MaxLiebe/Hydration-Tracker/src/arduino/hydration-tracker/logo.h

//To change the logo, convert an image to a resolution below 128x64. For the best results, also try to convert it to duo color (black & white).
//Now, use an online converter like https://www.online-utility.org/image/convert/to/XBM or https://convertio.co/png-xbm/ to convert your image to an XBM image.
//Open your downloaded XBM image in notepad and copy the array bytes to the LOGO_BITS array down below. Also make sure the resolution in LOGO_WIDTH and LOGO_HEIGHT is correct.

#define LOGO_WIDTH 120
#define LOGO_HEIGHT 58
static uint8_t LOGO_BITS[] = { 
0x00, 0x00, 0x00, 0x00, 0x00, 0x00, 0x00, 0x00, 0x00, 0x00, 0x00, 0x00, 
  0x00, 0x00, 0x00, 0x00, 0x00, 0x00, 0x00, 0x00, 0x00, 0x00, 0x00, 0x00, 
  0x00, 0x00, 0x00, 0x00, 0x00, 0x00, 0x00, 0x00, 0x00, 0x00, 0x00, 0x00, 
  0x00, 0x00, 0x00, 0x00, 0x00, 0x00, 0x00, 0x00, 0x00, 0x00, 0x00, 0x00, 
  0x00, 0x00, 0x00, 0x00, 0x00, 0x00, 0x00, 0x00, 0x00, 0x00, 0x00, 0x00, 
  0x00, 0x00, 0x00, 0x00, 0x00, 0x00, 0x00, 0x00, 0xD8, 0x0D, 0x00, 0x00, 
  0x00, 0x00, 0x00, 0x00, 0x00, 0x00, 0x00, 0x00, 0x00, 0x00, 0x00, 0x04, 
  0x00, 0x00, 0x00, 0x00, 0x00, 0x00, 0x00, 0x00, 0x00, 0x00, 0x00, 0x00, 
  0x00, 0x00, 0x04, 0x10, 0x00, 0x00, 0x00, 0x00, 0x00, 0x00, 0x00, 0x00, 
  0x00, 0x00, 0x00, 0x00, 0x00, 0x04, 0x10, 0x00, 0x00, 0x00, 0x00, 0x00, 
  0x00, 0x00, 0x00, 0x00, 0x00, 0x00, 0x00, 0x00, 0x04, 0x10, 0x00, 0x6C, 
  0x00, 0x00, 0x00, 0x00, 0x00, 0x00, 0x00, 0x00, 0x00, 0x00, 0x00, 0x08, 
  0x08, 0x00, 0x82, 0x00, 0x00, 0x00, 0x00, 0x00, 0x00, 0x00, 0x00, 0x00, 
  0x00, 0x00, 0x10, 0x04, 0x00, 0x82, 0x00, 0x00, 0x00, 0x00, 0x00, 0x00, 
  0x00, 0x00, 0x00, 0x00, 0x00, 0x20, 0x02, 0x00, 0x00, 0x00, 0x00, 0x00, 
  0x00, 0x00, 0x00, 0x00, 0x00, 0x00, 0x00, 0x00, 0x40, 0x01, 0x00, 0x81, 
  0x00, 0x00, 0x00, 0x00, 0x00, 0x00, 0x00, 0x00, 0x00, 0x00, 0x00, 0x80, 
  0x00, 0x00, 0x81, 0x00, 0x00, 0x00, 0x00, 0x00, 0x00, 0x00, 0x00, 0x00, 
  0x00, 0x00, 0x80, 0x00, 0x80, 0x61, 0x00, 0x00, 0x00, 0x00, 0x00, 0x00, 
  0x00, 0x00, 0x00, 0x00, 0x00, 0xC0, 0x01, 0xC0, 0x0C, 0x00, 0x00, 0x00, 
  0x00, 0x00, 0x00, 0x00, 0x00, 0x00, 0x00, 0x00, 0x40, 0x01, 0x40, 0x02, 
  0x00, 0x00, 0x00, 0x00, 0x00, 0x00, 0x00, 0x00, 0x00, 0x00, 0x00, 0xC0, 
  0x01, 0xC0, 0x01, 0x00, 0x00, 0x00, 0x00, 0x00, 0x00, 0x00, 0x00, 0x00, 
  0x00, 0x00, 0x00, 0x02, 0x20, 0x00, 0x00, 0x00, 0x00, 0x00, 0x00, 0x00, 
  0x00, 0x00, 0x00, 0x00, 0x00, 0x00, 0x04, 0x10, 0x00, 0x00, 0x00, 0x00, 
  0x00, 0x00, 0x00, 0x00, 0x00, 0x00, 0xC0, 0x07, 0x00, 0x14, 0x0A, 0x00, 
  0x54, 0x00, 0x00, 0x00, 0x00, 0x00, 0x00, 0x00, 0x00, 0xE0, 0x0F, 0x00, 
  0xD4, 0x0B, 0x00, 0x82, 0x00, 0x00, 0x00, 0x00, 0x00, 0x00, 0x00, 0x00, 
  0x20, 0x08, 0x00, 0x0C, 0x14, 0x00, 0x83, 0x01, 0x00, 0x00, 0x00, 0x00, 
  0x00, 0x00, 0x00, 0x20, 0x08, 0x00, 0x02, 0x24, 0x00, 0x82, 0x00, 0x00, 
  0x00, 0x00, 0x00, 0x00, 0x00, 0x00, 0x20, 0x08, 0x00, 0x01, 0x44, 0x00, 
  0x83, 0x01, 0x00, 0x00, 0x00, 0x00, 0x00, 0x00, 0x00, 0x20, 0x08, 0x80, 
  0x00, 0x84, 0x00, 0x82, 0x00, 0x00, 0x00, 0x00, 0xE0, 0xFF, 0xFE, 0xFD, 
  0x3F, 0x78, 0xFF, 0x07, 0x04, 0x01, 0x83, 0x01, 0x00, 0x00, 0x00, 0xF0, 
  0xFF, 0xFF, 0xFF, 0x3F, 0xF0, 0xFF, 0x0F, 0x04, 0x02, 0xFE, 0x00, 0x00, 
  0x00, 0x00, 0x10, 0x00, 0x01, 0x02, 0x20, 0x80, 0x00, 0x08, 0x04, 0x04, 
  0x54, 0x00, 0x00, 0x00, 0x00, 0x10, 0x00, 0x01, 0x02, 0x20, 0x80, 0x00, 
  0x08, 0x04, 0x08, 0x10, 0x00, 0x00, 0x00, 0x80, 0x11, 0x00, 0x01, 0x02, 
  0x20, 0x80, 0x00, 0x08, 0x04, 0x30, 0x38, 0x00, 0x00, 0x00, 0x00, 0x12, 
  0x00, 0x41, 0x82, 0x20, 0x80, 0x20, 0x08, 0x04, 0xC8, 0x2F, 0x00, 0x00, 
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
